penayush-tronics/Volt_reg/assets/image-1.png

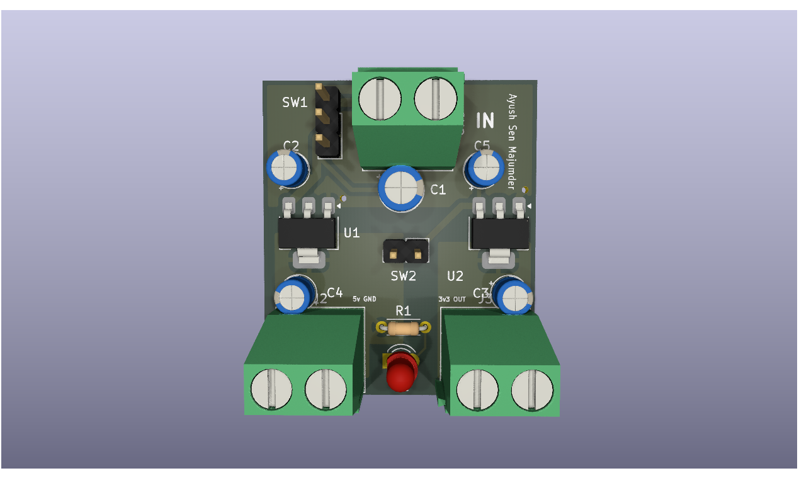
assets/image-1.png
